endlos99/flashrom99/avr/flashrom.c

/*
 * FlashROM 99
 *
 * A cartridge for the TI 99 that allows for running ROM images stored
 * on an SD card
 *
 * Copyright (c) 2016 Ralph Benzinger <r@0x01.de>
 *
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
 * You should have received a copy of the GNU General Public License
 * along with this program; if not, see <http://www.gnu.org/licenses/>.
 */


#include <stdint.h>

#include "loader.h"


int main(void)
{
  // setup cart
  init();

  // create menu loader
  uint8_t dl = genMenu();
  
  // wait for menu selection
  if (dl == 0)
    selectImage();

  // load selected image
  loadImage();

  // good night and good luck!
  while (1);
}
